piotr07da/Spotlight/Spotlight/src/DisplayLogo.h

#ifndef DISPLAY_LOGO_H
#define DISPLAY_LOGO_H

static const unsigned char PROGMEM DisplayLogo[] =
	{
		0b00000000,0b00000000,0b00000000,0b00000000,0b00000000,0b00000000,0b00000000,0b00000000,0b00000000,0b00000000,0b00000000,0b00000000,
        0b00000000,0b00000000,0b00000000,0b01111000,0b00000000,0b00000000,0b00000000,0b00000000,0b00000000,0b00000000,0b00000000,0b00000000,
        0b00000000,0b00000000,0b00000000,0b11110011,0b00000000,0b00000000,0b00000000,0b00000000,0b00000000,0b00000000,0b00000000,0b00000000,
        0b00000000,0b00000000,0b00000001,0b10111100,0b10000000,0b00000000,0b00000000,0b00000000,0b00000000,0b00000000,0b00000000,0b00000000,
        0b00000000,0b00000000,0b00000011,0b10111110,0b01000000,0b00000000,0b00000000,0b00000000,0b00000000,0b00000000,0b00000000,0b00000000,
        0b00000000,0b00000000,0b00000111,0b10111111,0b00100000,0b00000000,0b00000000,0b00000000,0b00000000,0b00000000,0b00000000,0b00000000,
        0b00000000,0b00000000,0b00000111,0b10111111,0b00000000,0b00000000,0b00000000,0b00000000,0b00000000,0b00000000,0b00000000,0b00000000,
        0b00000000,0b00000000,0b00001111,0b11111111,0b00100000,0b01000000,0b00000000,0b00000000,0b00000000,0b00000000,0b00000000,0b00000000,
        0b00000000,0b00000000,0b00001111,0b11111111,0b11011111,0b11000000,0b00000000,0b00000000,0b00000000,0b00000000,0b00000000,0b00000000,
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
        0b00000100,0b00000000,0b00000000,0b00000000,0b00000000,0b00000000,0b00000000,0b00000000,0b00000000,0b00000000,0b00000000,0b11000000,
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
};

#endif // DISPLAY_LOGO_H
