piotr07da/Spotlight/Spotlight/src/AudioSpectrumCalculator.h

#ifndef AUDIO_SPECTRUM_CALCULATOR_H
#define AUDIO_SPECTRUM_CALCULATOR_H

#include <Particle.h>

#include "AudioSampler.h"
#include "Messenger.h"

class AudioSpectrumCalculator
{
private:
	AudioSampler *_sampler;
	Messenger *_messenger;
	bool _enabled;
	float _spectrum[AudioSampler_SingleHalfBufferSize * 2];
	bool _spectrumReady;
	long _fftStart;

public:
	AudioSpectrumCalculator(AudioSampler *sampler, Messenger *messenger);

	void Setup();
	void Loop();

	void Enable();
	void Disable();
	float *Spectrum();
	bool SpectrumReady();
};

#endif // AUDIO_SPECTRUM_CALCULATOR_H
