piotr07da/Spotlight/Spotlight/src/AudioTrigger.h

#ifndef AUDIO_TRIGGER_H
#define AUDIO_TRIGGER_H

#include <Particle.h>

#include "AudioTriggerBandSelector.h"
#include "AudioSampler.h"
#include "AudioSpectrumCalculator.h"
#include "Messenger.h"

const uint16_t AudioTrigger_AmplitudeSpectrumSize = AudioSampler_SingleHalfBufferSize / 2;

class AudioTrigger
{
private:
	AudioSpectrumCalculator *_spectrumCalculator;
	Messenger *_messenger;
	bool _enabled;
	float _amplitudeSpectrumSquared[AudioTrigger_AmplitudeSpectrumSize];
	AudioTriggerBandSelector _bandSelector;
	bool _isTriggered;

public:
	AudioTrigger(AudioSpectrumCalculator *spectrumCalculator, Messenger *messenger);

	void Setup();
	void Loop();

	void Enable();
	void Disable();

	bool IsTriggered();
};

#endif // AUDIO_TRIGGER_H
