piotr07da/Spotlight/Spotlight/src/MasterMenuSubmenu.h

#ifndef MASTER_MENU_SUBMENU_H
#define MASTER_MENU_SUBMENU_H

enum class MasterMenuSubmenu
{
	FIRST = 0,
	GlobalPropertiesMenu = 0,
	SpotPropertiesMenu = 1,
	StandbyMenu = 2,
	HelpMenu = 3,
	LAST = 3,
	COUNT = 4,
};

#endif // MASTER_MENU_SUBMENU_H
