piotr07da/Spotlight/Spotlight/src/MenuSpotsNavigator.h

#ifndef MENU_SPOTS_NAVIGATOR_H
#define MENU_SPOTS_NAVIGATOR_H

#include "SpotCollection.h"
#include "Motor.h"

class MenuSpotsNavigator
{
private:
	SpotCollection *_spots;
	Motor *_motor;
	int _currentSpotIndex;

public:
	MenuSpotsNavigator(SpotCollection *spots, Motor *motor);

	SpotCollection *GetAll();
	int GetCount();
	Spot *GetCurrent();
	int GetCurrentIndex();
	void EnsureCurrentIndexInRange();
	void Prev();
	void Next();
	void RepositionToCurrent();
};

#endif // MENU_SPOT_NAVIGATOR_H
