piotr07da/Spotlight/Spotlight/src/SpotProperty.h

#ifndef SPOT_PROPERTY_H
#define SPOT_PROPERTY_H

enum class SpotProperty
{
	FIRST = 0,
	Position = 0,
	SpotTime = 1,
	SpotActivity = 2,
	TravelTime = 3,
	TravelActivity = 4,
	LAST = 4,
};

#endif // SPOT_PROPERTY_H
