piotr07da/Spotlight/Spotlight/src/LightActivity.h

#ifndef LIGHT_ACTIVITY_H
#define LIGHT_ACTIVITY_H

enum class LightActivity
{
	FIRST = 0,
	A_0 = 0,
	A_1 = 1,
	A_01 = 2,
	A_10 = 3,
	A_010 = 4,
	A_101 = 5,
	A_Strobe = 6,
	LAST = 6,
};

#endif // LIGHT_ACTIVITY_H
